BillyWoods/Narrowband-SDR/reverse_engineering/MSi001_implementation/0922-24.jpg

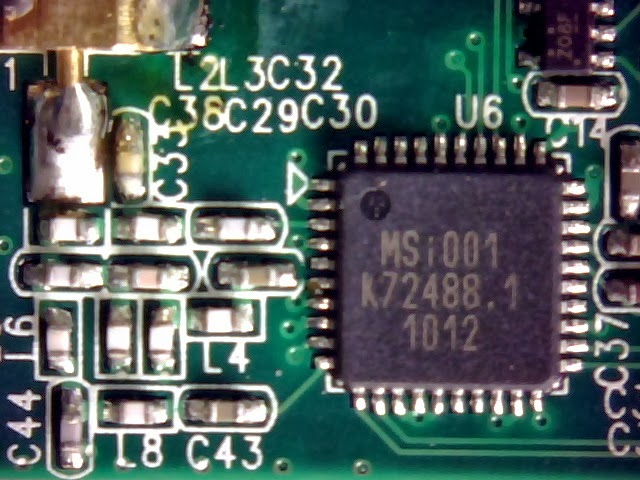
reverse_engineering/MSi001_implementation/0922-24.jpg
