BillyWoods/Narrowband-SDR/reverse_engineering/MSi001_implementation/0922-49.jpg

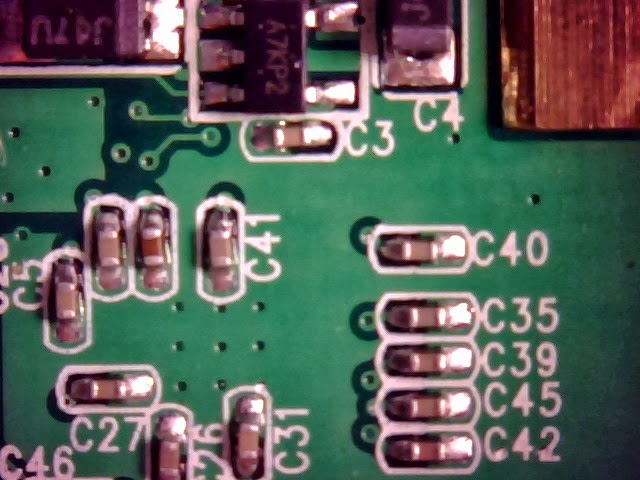
reverse_engineering/MSi001_implementation/0922-49.jpg
