BillyWoods/Narrowband-SDR/reverse_engineering/MSi001_implementation/IMG_20130922_193258.jpg

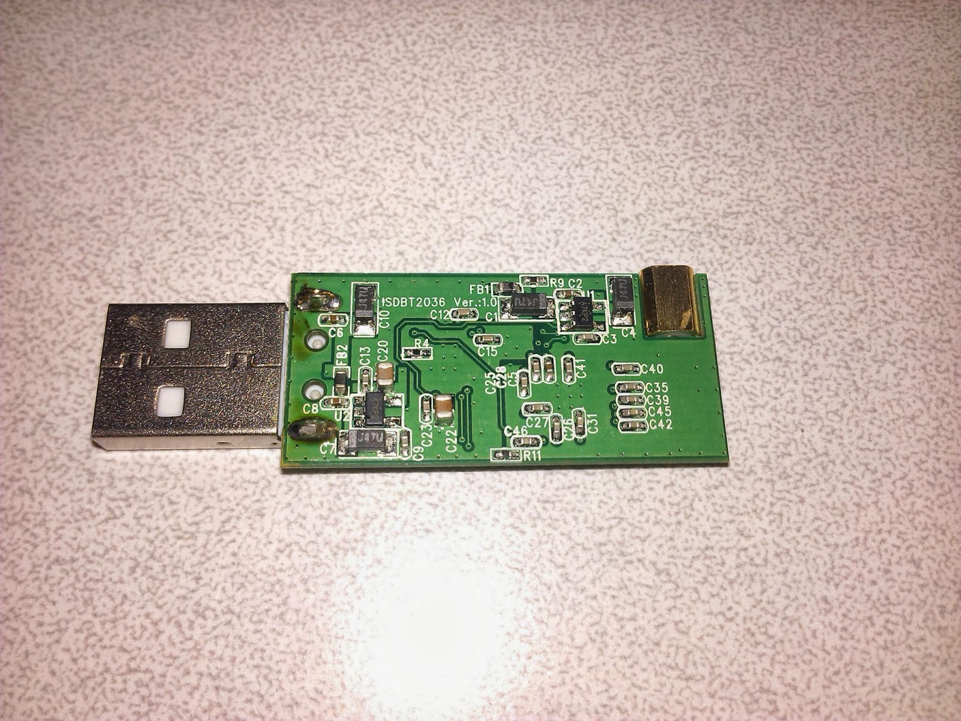
reverse_engineering/MSi001_implementation/IMG_20130922_193258.jpg
