BillyWoods/Narrowband-SDR/simulations/MSi001_VCO_stuff.asc

C1: cap; 2.7nF
C2: cap; 39nF
C3: cap; 2.7nF
I1: current; PULSE(0 .001 0ns 0 0 1ns 42ns); AC 1
I3: current; PULSE(0 -.001 39.5ns 0 0 1ns 80ns); AC 0
R1: res; 360
R2: res; 500
Named nets: 0, filter_input, filter_out
Loop filter pre-charge connects here?
(this allows fast charging of cap, bypassing R)
VCO_VCC connects here
Charge pump out
(this is to be filtered by the loop filter)
.ac dec 1000 1k 0.1G
This loop filter is based on the PLL reference design given for the ADF4351 
on pg. 25 of its datasheet. This topology is also very close to the one used on
the reverse-engineered Mirics TV dongle.
The charge pump output (phase detector) is probably somwhere around F_ref = 24 MHz.
