BillyWoods/Narrowband-SDR/simulations/differential_amp_and_pseudo_diff_input.asc

C1: cap; 16pF
C2: cap; 4pF
C3: cap; 200pF
R1: res; 40k
R2: res; 0
R3: res; 10k
R4: res; 20k
R5: res; 50
R6: res; 0
S1: sw; sampling
U2: AD8691
V1: voltage; SINE(0 0.75 1500k); AC 0.75 0; Rser=1k
V2: voltage; 1.65
V3: voltage; SINE(0 0.75 1500k 0 0 180); AC 1 180; Rser=1k
V4: voltage; 3.3
V5: voltage; 0
V6: voltage; PULSE(0 1 271n 0.0 0.0 62n 333n)
Named nets: 0, 3v3, neg, V_plus, V_neg, op_out, ADC_hold_cap, sample
.tran 0.00001
Pin capcitance
Hold
.model sampling SW(Ron=1 Roff=1Meg Vt=0.5)
