BillyWoods/Narrowband-SDR/simulations/antenna_input_coupling.asc

C1: cap
C2: cap
C3: cap
C4: cap
C5: cap
C6: cap; 1.4p
C7: cap
C8: cap
L1: ind
L2: ind
L3: ind
L4: ind
L5: ind
L6: ind
L7: ind
R1: res; 50R
R2: res; 90R
R3: res; 30R
R4: res; 75R
R5: res; 100R
R6: res; 100R
R7: res; 1K
V1: voltage; ""; AC 1
Named nets: 0
.ac dec 1000 0.15M 1900M
LNA (50 Ohm output)
64 - 108 MHz single-ended input
162 - 240 MHz single-ended input
470 - 970 MHz single-ended input
1000 - 1800 MHz single-ended input
AM input 2
0.15 - 30 MHz (nominal)
300 - 470 MHz (as a hack)
High-Z AM input
0.15 - 30 MHz single-ended input
TODO: connect up these other inputs
