BillyWoods/Narrowband-SDR/simulations/antenna_input_coupling_resistive_1.1.asc

C3: cap; 200pF
C6: cap; 1.4p
R1: res; 50R
R2: res; 90R
R3: res; 30R
R4: res; 75R
R5: res; 100R
R6: res; 100R
R7: res; 1K
R8: res; 25
R9: res; 25
R10: res; 50
R11: res; 25
V1: voltage; ""; AC 1
Named nets: 0, LNA_out, AM2_and_BAND3_input, BAND4/5_and_VHF_input, L_band_input
.ac dec 1000 0.03G 2G
LNA (50 Ohm output)
64 - 108 MHz single-ended input
(VHF)
162 - 240 MHz single-ended input
(Band 3)
470 - 970 MHz single-ended input
(Band 4/5)
1000 - 1800 MHz single-ended input
(L band)
AM input 2
0.15 - 30 MHz (nominal)
300 - 470 MHz (as a hack)
High-Z AM input
0.15 - 30 MHz single-ended input
