BillyWoods/Narrowband-SDR/simulations/antenna_input_coupling_2.asc

C1: cap; 200pF
C2: cap; 1nF
C3: cap; 200pF
C4: cap; 200pF
C5: cap; 200pF
C6: cap; 1.4p
C7: cap; 200pF
C8: cap; 200pF
C9: cap; 1nF
C10: cap; 200pF
C11: cap; 200pF
C12: cap; 200pF
C13: cap; 18pF
L1: ind; 80nH
R1: res; 50R
R2: res; 90R
R3: res; 30R
R4: res; 75R
R5: res; 100R
R6: res; 100R
R7: res; 1K
V1: voltage; ""; AC 1
Named nets: 0
.ac dec 1000 150k 2G
LNA (50 Ohm output)
64 - 108 MHz single-ended input
(50-120MHz)
162 - 240 MHz single-ended input
(108 - 250MHz or 108 - 380MHz??)
470 - 970 MHz single-ended input
(380 - 1000MHz)
1000 - 1800 MHz single-ended input
(1000-2400MHz)
AM input 2
0.15 - 30 MHz (nominal)
250-380 MHz (as a hack)
High-Z AM input
0.15 - 30 MHz single-ended input
This High-Z input has been connected up before the LNA to bypass it.
