BillyWoods/Narrowband-SDR/simulations/LNA_coupling.asc

C1: cap; 99pF; V=25 Irms=0 Rser=0 Lser=0
C2: cap; 100pF; V=25 Irms=0 Rser=0 Lser=0
C3: cap; 1nF; V=25 Irms=0 Rser=0 Lser=0
C4: cap; 0.1µF; V=25 Irms=0 Rser=0 Lser=0
L1: ind; 900pH
L2: ind; 1000pH
L3: ind; 150nH; Rser=3 Cpar=0.8pF
L4: ind; 150nH; Rser=3 Cpar=0.8pF
R1: res; 50
R2: res; 1k
R3: res; 50
V1: voltage; ""; AC 1; Rser=50
Named nets: 0
.ac dec 100 100k 3G
https://www.avx.com/docs/techinfo/CeramicCapacitors/parasitc.pdf
 
^ Indicates that 1000pH of inductance would be reasonable for an SMD ceramic  capacitor about 500 times larger than what we have here.
It seems that inductance is mostly a function of the package.
 
So surely we're safe.
High-Z input (for 0 - 30 MHz)
