BillyWoods/Narrowband-SDR/fx2fw/fx2sdr/fw.c

/**
 * Copyright (C) 2009 Ubixum, Inc. 
 *
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
 * You should have received a copy of the GNU Lesser General Public
 * License along with this library; if not, write to the Free Software
 * Foundation, Inc., 51 Franklin Street, Fifth Floor, Boston, MA  02110-1301  USA
 **/

#include <fx2macros.h>
#include <fx2ints.h>
#include <autovector.h>
#include <delay.h>
#include <setupdat.h>

#ifdef DEBUG_FIRMWARE 
#include <serial.h>
#include <stdio.h>
#else
#define printf(...)
#endif

#include "fw.h"



volatile __bit dosuspend=FALSE;
volatile __bit got_sud=FALSE;

// custom functions
extern void main_loop();
extern void main_init();


void main() {

 main_init();
 
 while(TRUE) {

     main_loop();

     if (got_sud) {
       got_sud=FALSE;
       handle_setupdata();
     }

     if (dosuspend) {
        dosuspend=FALSE;
        do {
           printf ( "I'm going to Suspend.\n" );
           WAKEUPCS |= bmWU|bmWU2; // make sure ext wakeups are cleared
           SUSPEND=1;
           PCON |= 1;
           __asm
           nop
           nop
           nop
           nop
           nop
           nop
           nop
           __endasm;
        } while ( !remote_wakeup_allowed && REMOTE_WAKEUP()); 
        printf ( "I'm going to wake up.\n");

        // resume
        // trm 6.4
        if ( REMOTE_WAKEUP() ) {
            delay(5);
            USBCS |= bmSIGRESUME;
            delay(15);
            USBCS &= ~bmSIGRESUME;
        }

     }

 } // end while

} // end main

void resume_isr() __interrupt RESUME_ISR {
 CLEAR_RESUME();
}
  
void sudav_isr() __interrupt SUDAV_ISR {
 got_sud=TRUE;
 CLEAR_SUDAV();
}
void usbreset_isr() __interrupt USBRESET_ISR {
 handle_hispeed(FALSE);
 CLEAR_USBRESET();
}
void hispeed_isr() __interrupt HISPEED_ISR {
 handle_hispeed(TRUE);
 CLEAR_HISPEED();
}

void suspend_isr() __interrupt SUSPEND_ISR {
 dosuspend=TRUE;
 CLEAR_SUSPEND();
}

// predef; definition is in device.c
//
// Per SDCC manual: a prototype of the isr MUST be present or included
// in the file that contains the function main.
//
// Otherwise this interrupt won't be included in the interrupt vector table
void timer2_isr(void) __interrupt TF2_ISR; 
void ibn_isr(void) __interrupt IBN_ISR;
void gpifwf_isr(void) __interrupt GPIFWF_ISR;
